jshook/p2_p2_cube/3d_models/snap_joint_after_cap.png

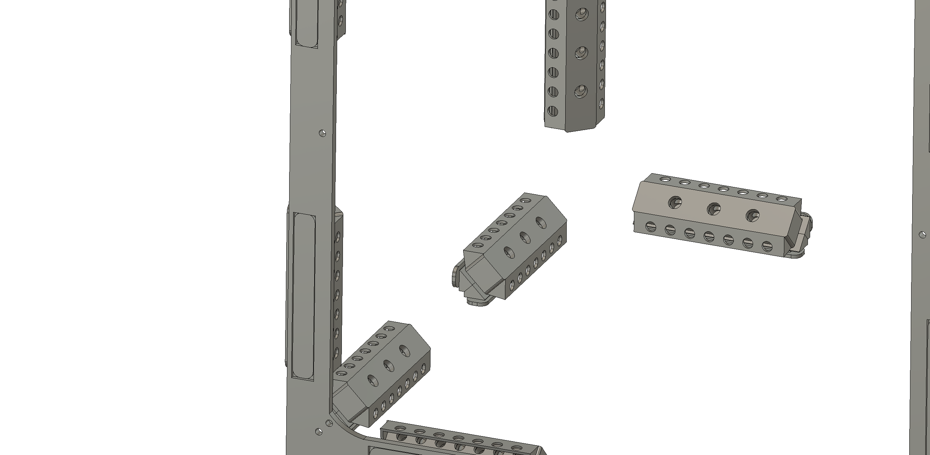
3d_models/snap_joint_after_cap.png
